algofoogle/tt06-grab-bag/xschem/simulation/tb_inverter.spice

** sch_path: /home/anton/projects/tt06-grab-bag/xschem/tb_inverter.sch
**.subckt tb_inverter
x1 net1 VSS A Y inverter
Vvss VSS GND 0
Vvdd VDD GND dc 1.8V pwl( 0ns 0V 2ns 0V 25ns 1.8V 175ns 1.8V 198ns 0V )
Va A GND pulse( 0V 1.8V 0ns 0.5ns 0.5ns 20ns 40ns )
R1 OUT Y 500 m=1
C1 Y VSS 2.5p m=1
C2 OUT VSS 2.5p m=1
Vmeas VDD net1 0
.save i(vmeas)
x2 net2 VSS A Y_parax inverter_parax
R2 OUT_parax Y_parax 500 m=1
C3 Y_parax VSS 2.5p m=1
C4 OUT_parax VSS 2.5p m=1
Vmeas1 VDD net2 0
.save i(vmeas1)
**** begin user architecture code

** opencircuitdesign pdks install
.lib /home/anton/.volare/volare/sky130/versions/bdc9412b3e468c102d01b7cf6337be06ec6e9c9a/sky130A/libs.tech/ngspice/sky130.lib.spice tt_mm





.options savecurrents
.control
  repeat 5
    save all
    tran 10ps 200ns
    write tb_inverter.raw
    set appendwrite
    reset
  end
.endc



**** end user architecture code
**.ends

* expanding   symbol:  inverter.sym # of pins=4
** sym_path: /home/anton/projects/tt06-grab-bag/xschem/inverter.sym
** sch_path: /home/anton/projects/tt06-grab-bag/xschem/inverter.sch
.subckt inverter VDD VSS A Y
*.iopin VDD
*.iopin VSS
*.ipin A
*.opin Y
XM1 Y A VDD VDD sky130_fd_pr__pfet_01v8 L=0.15 W=8 nf=1 ad='int((nf+1)/2) * W/nf * 0.29' as='int((nf+2)/2) * W/nf * 0.29' pd='2*int((nf+1)/2) * (W/nf + 0.29)'
+ ps='2*int((nf+2)/2) * (W/nf + 0.29)' nrd='0.29 / W' nrs='0.29 / W' sa=0 sb=0 sd=0 mult=1 m=1
XM2 Y A VSS VSS sky130_fd_pr__nfet_01v8 L=0.15 W=4 nf=1 ad='int((nf+1)/2) * W/nf * 0.29' as='int((nf+2)/2) * W/nf * 0.29' pd='2*int((nf+1)/2) * (W/nf + 0.29)'
+ ps='2*int((nf+2)/2) * (W/nf + 0.29)' nrd='0.29 / W' nrs='0.29 / W' sa=0 sb=0 sd=0 mult=1 m=1
.ends


* expanding   symbol:  inverter_parax.sym # of pins=4
** sym_path: /home/anton/projects/tt06-grab-bag/xschem/inverter.sym
.include /home/anton/projects/tt06-grab-bag/mag/inverter.sim.spice
.GLOBAL GND
.end
