algofoogle/tt06-grab-bag/pcb/tt06-vga-opamp/jumper-nc-spice/jumper-nc.spice

.subckt jumper-nc 1 2
Rjumper 1 2 0.001
.ends
