algofoogle/tt06-grab-bag/verilog/gl/controller.v

module controller (VGND,
    VPWR,
    b6,
    b7,
    clk,
    g6,
    g7,
    hblank,
    hsync,
    r6,
    r7,
    rst_n,
    vblank,
    vsync,
    b,
    g,
    r,
    ui_in);
 input VGND;
 input VPWR;
 output b6;
 output b7;
 input clk;
 output g6;
 output g7;
 output hblank;
 output hsync;
 output r6;
 output r7;
 input rst_n;
 output vblank;
 output vsync;
 output [7:0] b;
 output [7:0] g;
 output [7:0] r;
 input [7:0] ui_in;

 wire _0000_;
 wire _0001_;
 wire _0002_;
 wire _0003_;
 wire _0004_;
 wire _0005_;
 wire _0006_;
 wire _0007_;
 wire _0008_;
 wire _0009_;
 wire _0010_;
 wire _0011_;
 wire _0012_;
 wire _0013_;
 wire _0014_;
 wire _0015_;
 wire _0016_;
 wire _0017_;
 wire _0018_;
 wire _0019_;
 wire _0020_;
 wire _0021_;
 wire _0022_;
 wire _0023_;
 wire _0024_;
 wire _0025_;
 wire _0026_;
 wire _0027_;
 wire _0028_;
 wire _0029_;
 wire _0030_;
 wire _0031_;
 wire _0032_;
 wire _0033_;
 wire _0034_;
 wire _0035_;
 wire _0036_;
 wire _0037_;
 wire _0038_;
 wire _0039_;
 wire _0040_;
 wire _0041_;
 wire _0042_;
 wire _0043_;
 wire _0044_;
 wire _0045_;
 wire _0046_;
 wire _0047_;
 wire _0048_;
 wire _0049_;
 wire _0050_;
 wire _0051_;
 wire _0052_;
 wire _0053_;
 wire _0054_;
 wire _0055_;
 wire _0056_;
 wire _0057_;
 wire _0058_;
 wire _0059_;
 wire _0060_;
 wire _0061_;
 wire _0062_;
 wire _0063_;
 wire _0064_;
 wire _0065_;
 wire _0066_;
 wire _0067_;
 wire _0068_;
 wire _0069_;
 wire _0070_;
 wire _0071_;
 wire _0072_;
 wire _0073_;
 wire _0074_;
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
    .VGND(VGND),
    .VNB(VGND),
    .VPB(VPWR),
    .VPWR(VPWR),
    .X(_0276_));
 sky130_fd_sc_hd__buf_1 _0766_ (.A(\rampc[0] ),
    .VGND(VGND),
    .VNB(VGND),
    .VPB(VPWR),
    .VPWR(VPWR),
    .X(_0277_));
 sky130_fd_sc_hd__inv_2 _0767_ (.A(registered),
    .VGND(VGND),
    .VNB(VGND),
    .VPB(VPWR),
    .VPWR(VPWR),
    .Y(_0278_));
 sky130_fd_sc_hd__nand2_1 _0768_ (.A(gate),
    .B(_0278_),
    .VGND(VGND),
    .VNB(VGND),
    .VPB(VPWR),
    .VPWR(VPWR),
    .Y(_0279_));
 sky130_fd_sc_hd__buf_1 _0769_ (.A(_0279_),
    .VGND(VGND),
    .VNB(VGND),
    .VPB(VPWR),
    .VPWR(VPWR),
    .X(_0280_));
 sky130_fd_sc_hd__buf_1 _0770_ (.A(_0280_),
    .VGND(VGND),
    .VNB(VGND),
    .VPB(VPWR),
    .VPWR(VPWR),
    .X(_0281_));
 sky130_fd_sc_hd__dlymetal6s2s_1 _0771_ (.A(_0278_),
    .VGND(VGND),
    .VNB(VGND),
    .VPB(VPWR),
    .VPWR(VPWR),
    .X(_0282_));
 sky130_fd_sc_hd__o22a_1 _0772_ (.A1(_0282_),
    .A2(_0099_),
    .B1(_0139_),
    .B2(_0275_),
    .VGND(VGND),
    .VNB(VGND),
    .VPB(VPWR),
    .VPWR(VPWR),
    .X(_0283_));
 sky130_fd_sc_hd__buf_1 _0773_ (.A(_0107_),
    .VGND(VGND),
    .VNB(VGND),
    .VPB(VPWR),
    .VPWR(VPWR),
    .X(_0284_));
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
